kuato781/vbar-stand/documentation/product-images/01-components.jpg

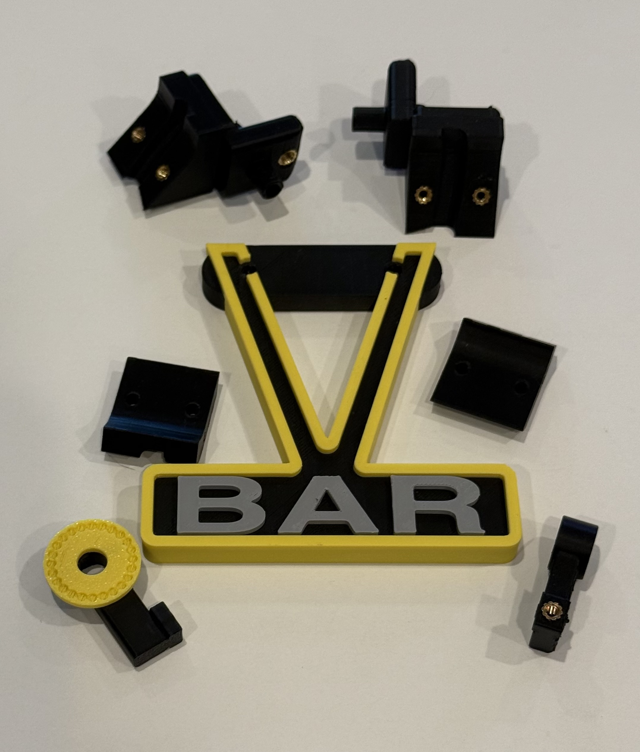
documentation/product-images/01-components.jpg
