kuato781/vbar-stand/stl-scad/VBar-SMUT-left-cap.scad

// Fit-tested 2.3 cap. For dimensional changes, rebuild from the measured geometry;
// OpenSCAD add/remove modules make local edits against the exact mesh.
module add_material() {}
module remove_material() {}
difference() {
    union() {
        import("VBar-SMUT-left-cap.stl",convexity=10);
        add_material();
    }
    remove_material();
}
