kuato781/vbar-stand/stl-scad/VBar-SMUT-stand-assembly-preview.scad

// Preview the three stand color parts at their shared assembly origin.
// Export/print the individual SCAD or STL parts, not this combined preview.
color([0.06,0.06,0.06]) import("VBar-SMUT-Stand-HEADER-CORE.stl",convexity=10);
color([0.98,0.66,0.04]) import("VBar-SMUT-Stand-WRAP.stl",convexity=10);
color([0.78,0.78,0.78]) import("VBar-SMUT-Stand-BAR.stl",convexity=10);
