kuato781/vbar-stand/documentation/product-images/02-assembled.jpg

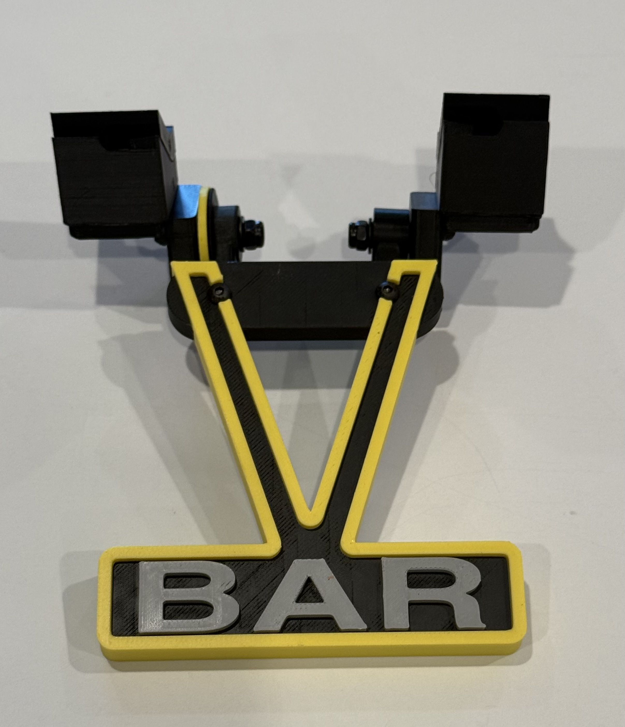
documentation/product-images/02-assembled.jpg
